BBC-Tech-Education/Team-Hyperion/Legacy Team Hyperion Files/2021 - The Dreamteam - Matthew Adams and Sam Garg (OnStage Novice)/Robotics Mr beast vs Dream.docx

# Robotics Mr beast vs Dream

# What will our performance look like?

Our performance will be a fight and dance scene between 2 robots (Mr beast vs Dream). We will have 3 motors and will be a touch sensor (will be located with the shield (if button is pushed then the sword will come down)) an ultrasonic sensor (eyes for the head (if robot is seen then activate code which does if touch sensor is pushed)) and a colour sensor (located near the wheels (will be used just in case the robot accidently runs out of the square)). They start in a corner, firstly, we will have a repeat of a forward walking movement, followed by a slow smooth forward movement. We will then raise the arm, and will have 3 short sharp movements forward, then we will move the arm back down and have three short sharp movements. Then we will move forward and backwards, followed by a smooth turn. (unprogrammed***) Then we will have the arm raised and then we will have 3 90* rotations anti and positive clockwise. Then we will have the sword go down and then up again quickly and we will have the robots go back and forward many times intensely and fast. Then we will have them fight for some time and then Dream will Defeat Mr Beast and will walk away slowly, that is it. (All was synchronised, but they were coming from opposite sides).
