BBC-Tech-Education/Team-Hyperion/Legacy Team Hyperion Files/2021 - The Dreamteam - Matthew Adams and Sam Garg (OnStage Novice)/Project 2/Ready/FINAL/STATES and NATIONALS CHECKLIST.docx

# STATES and NATIONALS CHECKLIST:

# Sam:

## Off Stage

Make sure that the program looks right |_|

Make sure that all sensors/motor ports are plugged in |_|

Make sure that you have done at least 1 perfect performance |_|

## On Stage

Make sure that all sensors/motors ports are plugged in |_|

# Matthew:

## Off Stage

Make sure that all sensors/motor ports are plugged in |_|

Make sure that you have done at least 1 perfect performance |_|

Make sure the robots are all connected properly |_|

## On Stage

Make sure that all sensors/motor ports are plugged in |_|

# Chris:

## Off Stage

Make sure that all sensors/motor ports are plugged in |_|

Make sure that you have done at least 1 perfect performance |_|

Make sure that all props are connected and ready for the performance |_|

## On Stage

Start setting up the props and get ready to start dancing |_|
