BBC-Tech-Education/Team-Hyperion/2024 - Team Hyperion (Soccer Infrared)/Documentation/tssp_system_library.png

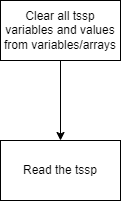
2024 - Team Hyperion (Soccer Infrared)/Documentation/tssp_system_library.png
