BBC-Tech-Education/Team-Hyperion/2025 - Team Hyperion (Soccer Infrared)/Software/src/junpenghaung.jpg

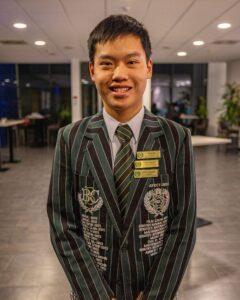
2025 - Team Hyperion (Soccer Infrared)/Software/src/junpenghaung.jpg
