BBC-Tech-Education/Team-Hyperion/2025 - Team Hyperion (Soccer Infrared)/Software/src/Teensy Pinout Schematic.jpeg

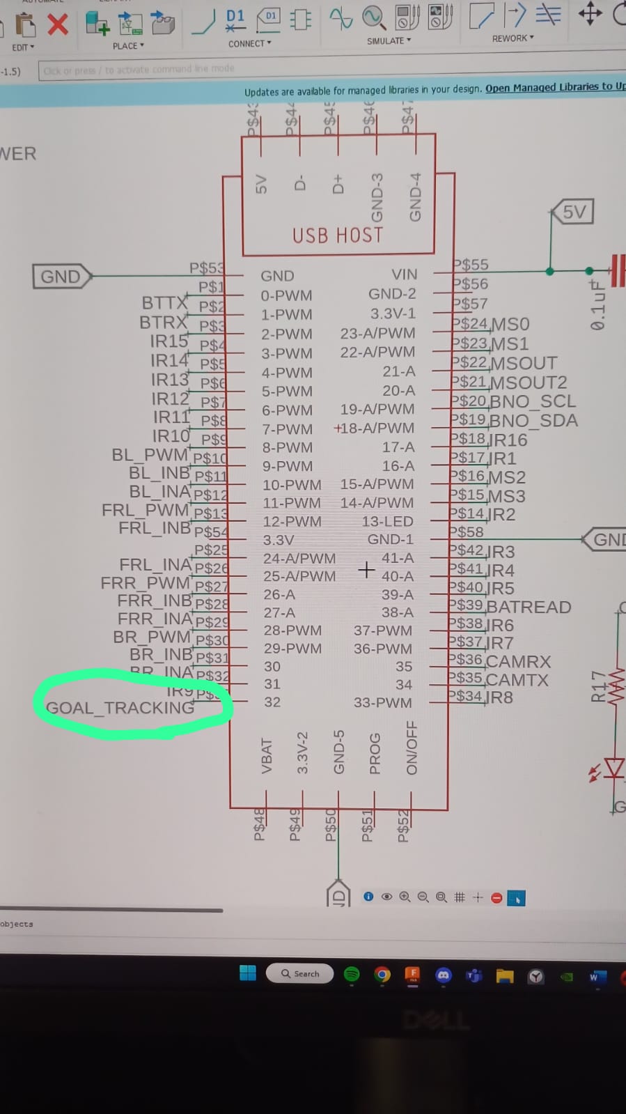
2025 - Team Hyperion (Soccer Infrared)/Software/src/Teensy Pinout Schematic.jpeg
