BBC-Tech-Education/Team-Hyperion/2026 - Team Hyperion (Soccer Infrared + Soccer Vision)/Documentation/Portrait Photos/SGARG.jpg

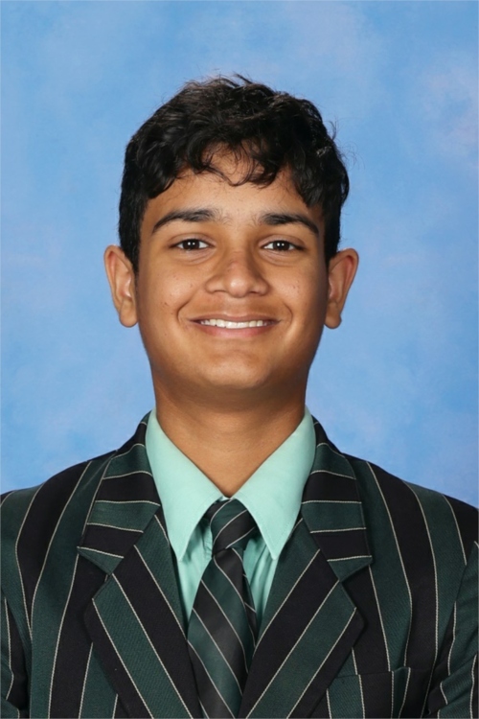
2026 - Team Hyperion (Soccer Infrared + Soccer Vision)/Documentation/Portrait Photos/SGARG.jpg
