BBC-Tech-Education/Team-Hyperion/2026 - Team Hyperion (Soccer Infrared + Soccer Vision)/Documentation/Portrait Photos/TMCCABE.jpg

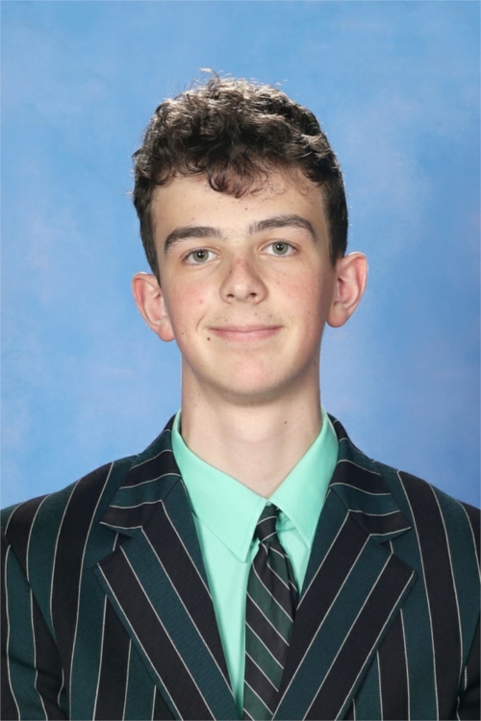
2026 - Team Hyperion (Soccer Infrared + Soccer Vision)/Documentation/Portrait Photos/TMCCABE.jpg
