BBC-Tech-Education/Team-Hyperion/2026 - Team Hyperion (Soccer Infrared + Soccer Vision)/Hardware/Robot Design Photos/Screenshot 2026-06-05 101610.png

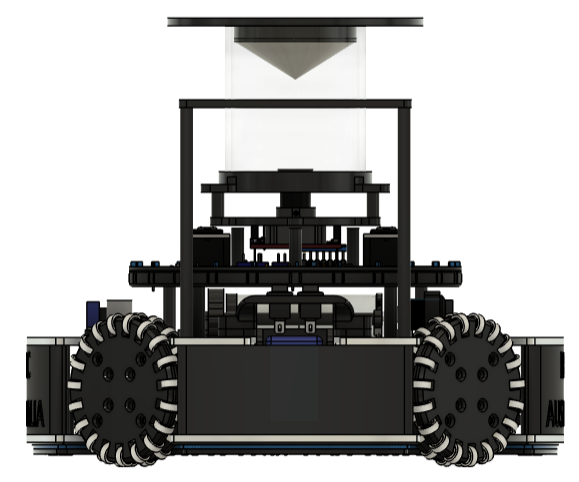
2026 - Team Hyperion (Soccer Infrared + Soccer Vision)/Hardware/Robot Design Photos/Screenshot 2026-06-05 101610.png
