BBC-Tech-Education/Team-Hyperion/2026 - Team Hyperion (Soccer Infrared + Soccer Vision)/Software/Primary/src/hall of fame/ashtontr.png

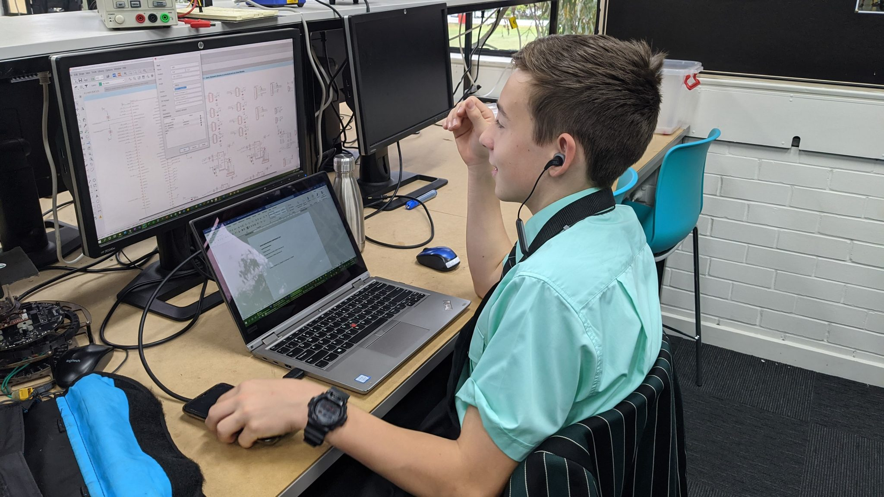
2026 - Team Hyperion (Soccer Infrared + Soccer Vision)/Software/Primary/src/hall of fame/ashtontr.png
