BBC-Tech-Education/Team-Hyperion/2026 - Team Hyperion (Soccer Infrared + Soccer Vision)/Software/Primary/src/PrimaryTeensySchematicupdated.png

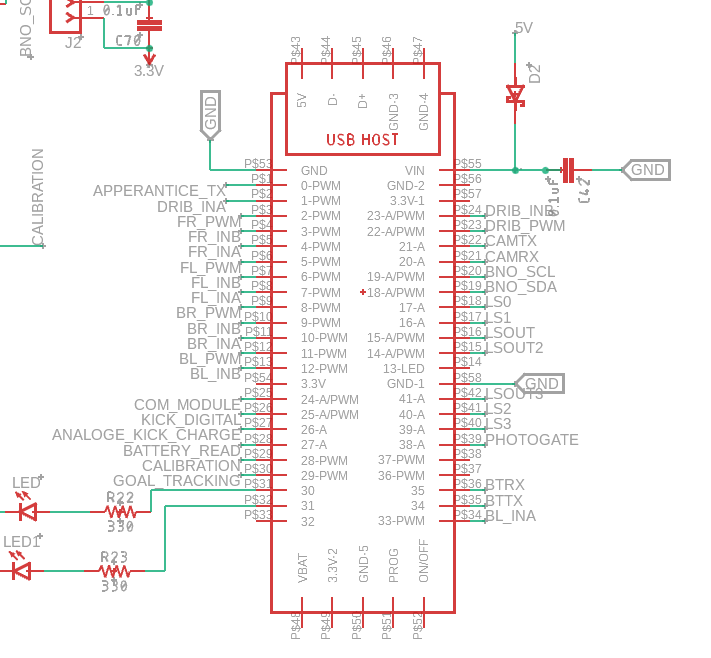
2026 - Team Hyperion (Soccer Infrared + Soccer Vision)/Software/Primary/src/PrimaryTeensySchematicupdated.png
